maarten-pennings/WordClock/imgs/3v3-5v0-schem.png

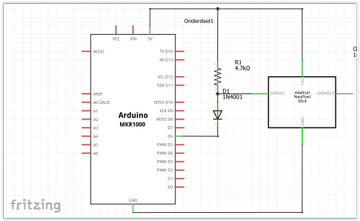
imgs/3v3-5v0-schem.png
