maarten-pennings/WordClock/imgs/3v3-5v0-scope.png

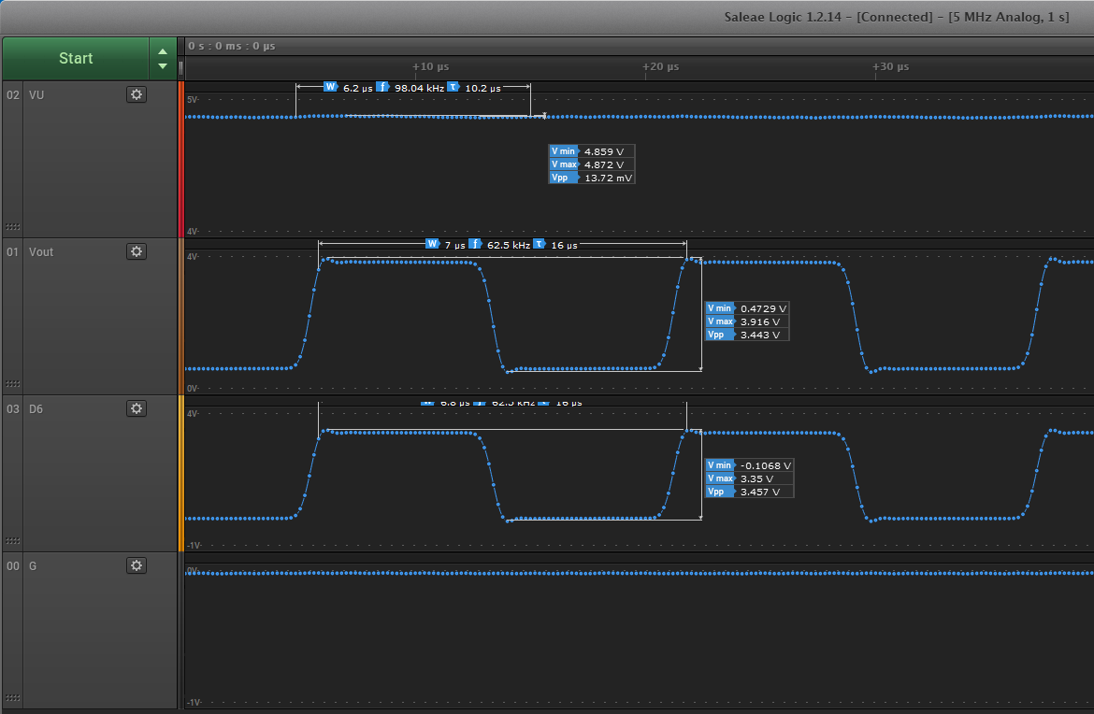
imgs/3v3-5v0-scope.png
